SP5GW/RF_Tap/img/IMG_1132.jpg

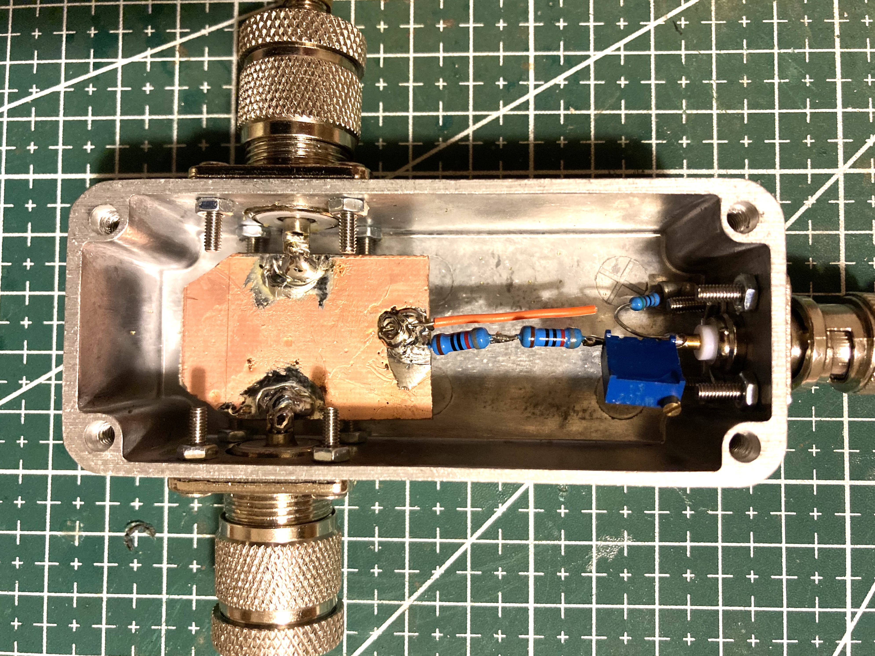
img/IMG_1132.jpg
