SP5GW/RF_Tap/meas/S21_RF_Input_RF_Tap_noCap_UnTerm2024-03-03 11-43-42.png

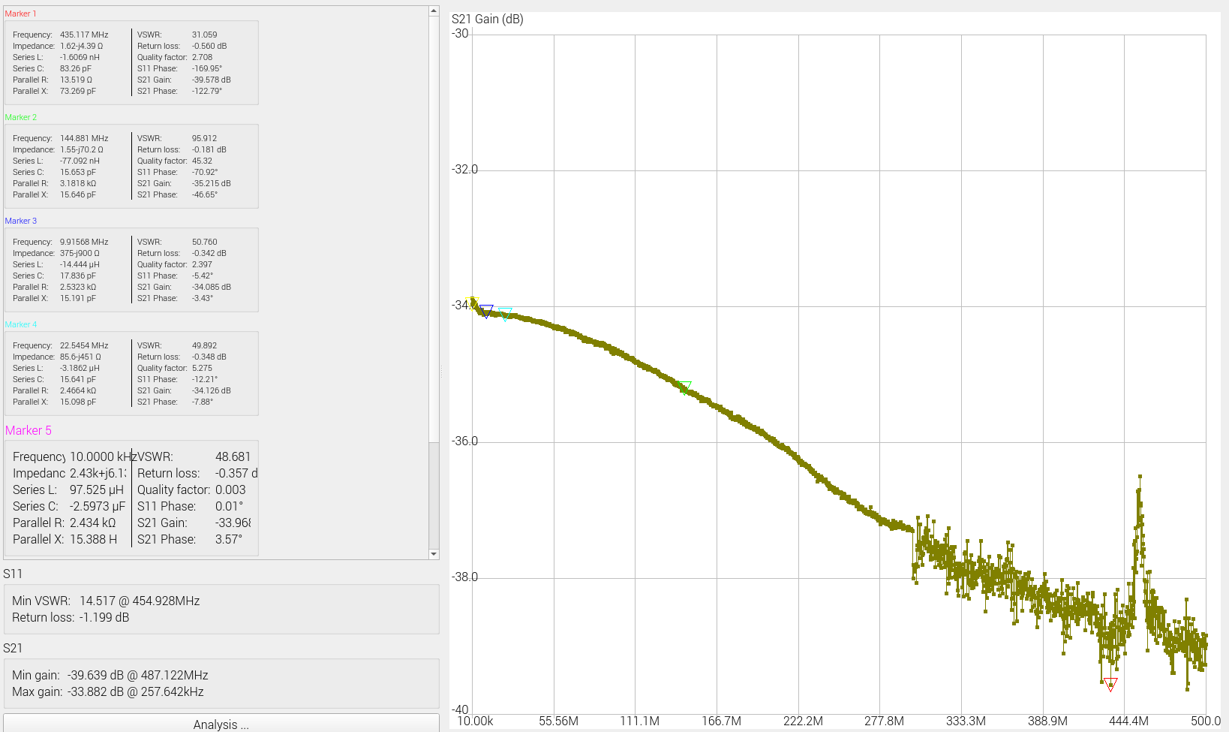
meas/S21_RF_Input_RF_Tap_noCap_UnTerm2024-03-03 11-43-42.png
