SP5GW/RF_Tap/sim/RFTap_v1_calibration_circuit.asc

Rs_nanovna_ch0: res; 50
Rs_nanovna_ch1: res; 50
V1: signal; AC 1
Named nets: 0, v1, Uin
.ac dec 1000 1k 100Meg
.step param R list 100Meg 50
.param R 5000
1) NanoVNA Callibration Circuit (through)
Calibration_Adj = Uin/v1 = 0.5/1=0.5 (-6dB)
