SP5GW/RF_Tap/sim/RFTap_v1_terminated_RF_Path.asc

DummyLoad: res; 50
R2: res; 51
R3: res; 2500
Rs_nanovna_ch0: res; 50
Rs_nanovna_ch1: res; 50
V1: signal; AC 2
Named nets: 0, v1, Uin, Utap
.ac dec 1000 1k 500Meg
3) NanoVNA S21 measurement (RF Path terminated with 50 ohm load)
Uin/v1 = 0.5/1=0.5 (-6dB) => Calibration_Adjustment = 6dB
V1 = 1V
Uin = 0.4951V
Utap = 4.951mV
Utap/V1 = 0.04951 (-46.106dB)
 
Logmag_NanoVna_Reading [dB] = Utap/V1 [dB] + 
Calibration_Adjustment [dB] = -46.106 + 6 = -40.106dB
 
Utap/Uin = 0.01 (-40dB)
