SP5GW/RF_Tap/sim/RFTap_v1_terminated_RF_Path_100W.asc

DummyLoad: res; 50
R1a: res; 820
R1b: res; 820
R1c: res; 820
R2: res; 51
Rs_nanovna_ch0: res; 50
Rs_nanovna_ch1: res; 50
V1: voltage; 100
Named nets: 0, v1, Uin, Utap, Vr1a, Vr1b
4) Resistor Power Rating Calculation
.op
Power dissipated in a purely resistive load fed from an AC rms supply 
is the same as that for a resistor connected to a DC supply and is 
given as, i.e.:
P = Urms*Irms where Irms = Urms/R
this gives:
P=Urms^2/R
 
Urms = Upk / SQRT(2) where Upk is peak voltage, while Urms is 
root-mean-sqaure voltage
.tran 5u
For instantaneous power Ppk=100W and 50ohm resistive load:
 
Upk = SQRT(Ppk*R) = SQRT(100*50) = 70.7V
Urms = Upk/SQRT(2) = SQRT(Ppk*R/2) = SQRT(100*50/2) = 50V
 
If Urms applied to dummylaod = 50V then the power disipating 
on resistor network is:
 
Prms(R1a or R1b or R1c) = 325mW (minimum R1a, R1b, R1c  resistor rating is 500mW)
Prms(R2) = 5mW (minimum R2 resistor rating can be 125mW)
