SP5GW/RF_Tap/sim/RFTap_v1_terminated_RF_Path_FreqDepLoss.asc

C: cap; {x}
Cparasitic: cap; 14p
DummyLoad: res; 50
R1a: res; 820
R1b: res; 820
R1c: res; 820
R2: res; 51
Rs_nanovna_ch0: res; 50
Rs_nanovna_ch1: res; 50
V1: signal; AC 2
Named nets: 0, v1, Uin, Utap
.ac dec 1000 1Meg 500Meg
3) NanoVNA S21 measurement (RF Path terminated with 50 ohm load) - frequency dependent loss
f=3.52MHz   => -40.1dB
f=144.0MHz => -40.5dB
f=435.1MHz => -42.9dB
.step param x list 0.00001p 0.7p
