SP5GW/RF_Tap/sim/RFTap_v1_unterminated_RF_Path.asc

R2: res; 51
R3: res; 2500
Rs_nanovna_ch0: res; 50
Rs_nanovna_ch1: res; 50
V1: signal; AC 1
Named nets: 0, v1, Uin, Utap
.ac dec 1000 1k 100Meg
2) NanoVNA S21 measurement (RF Path unterminated)
Uin/v1 = 0.5/1=0.5 (-6dB) => Calibration_Adjustment = 6dB
V1 = 1V
Uin = 0.981V
Utap = 9.804mV
Utap/V1 = 0.09804 ( -40.172dB)
Logmag_NanoVna_Reading [dB] = Utap/V1 [dB] + Calibration_Adjustment [dB] = 
-40.172 + 6 = -34.172dB
 
Utap/Uin = 0.01 (-40dB)
