SP5GW/RF_Tap/schematics/RF_Tap_Schematics.kicad_sch

## KiCad design schematics/RF_Tap_Schematics.kicad_sch (2024-03-12)

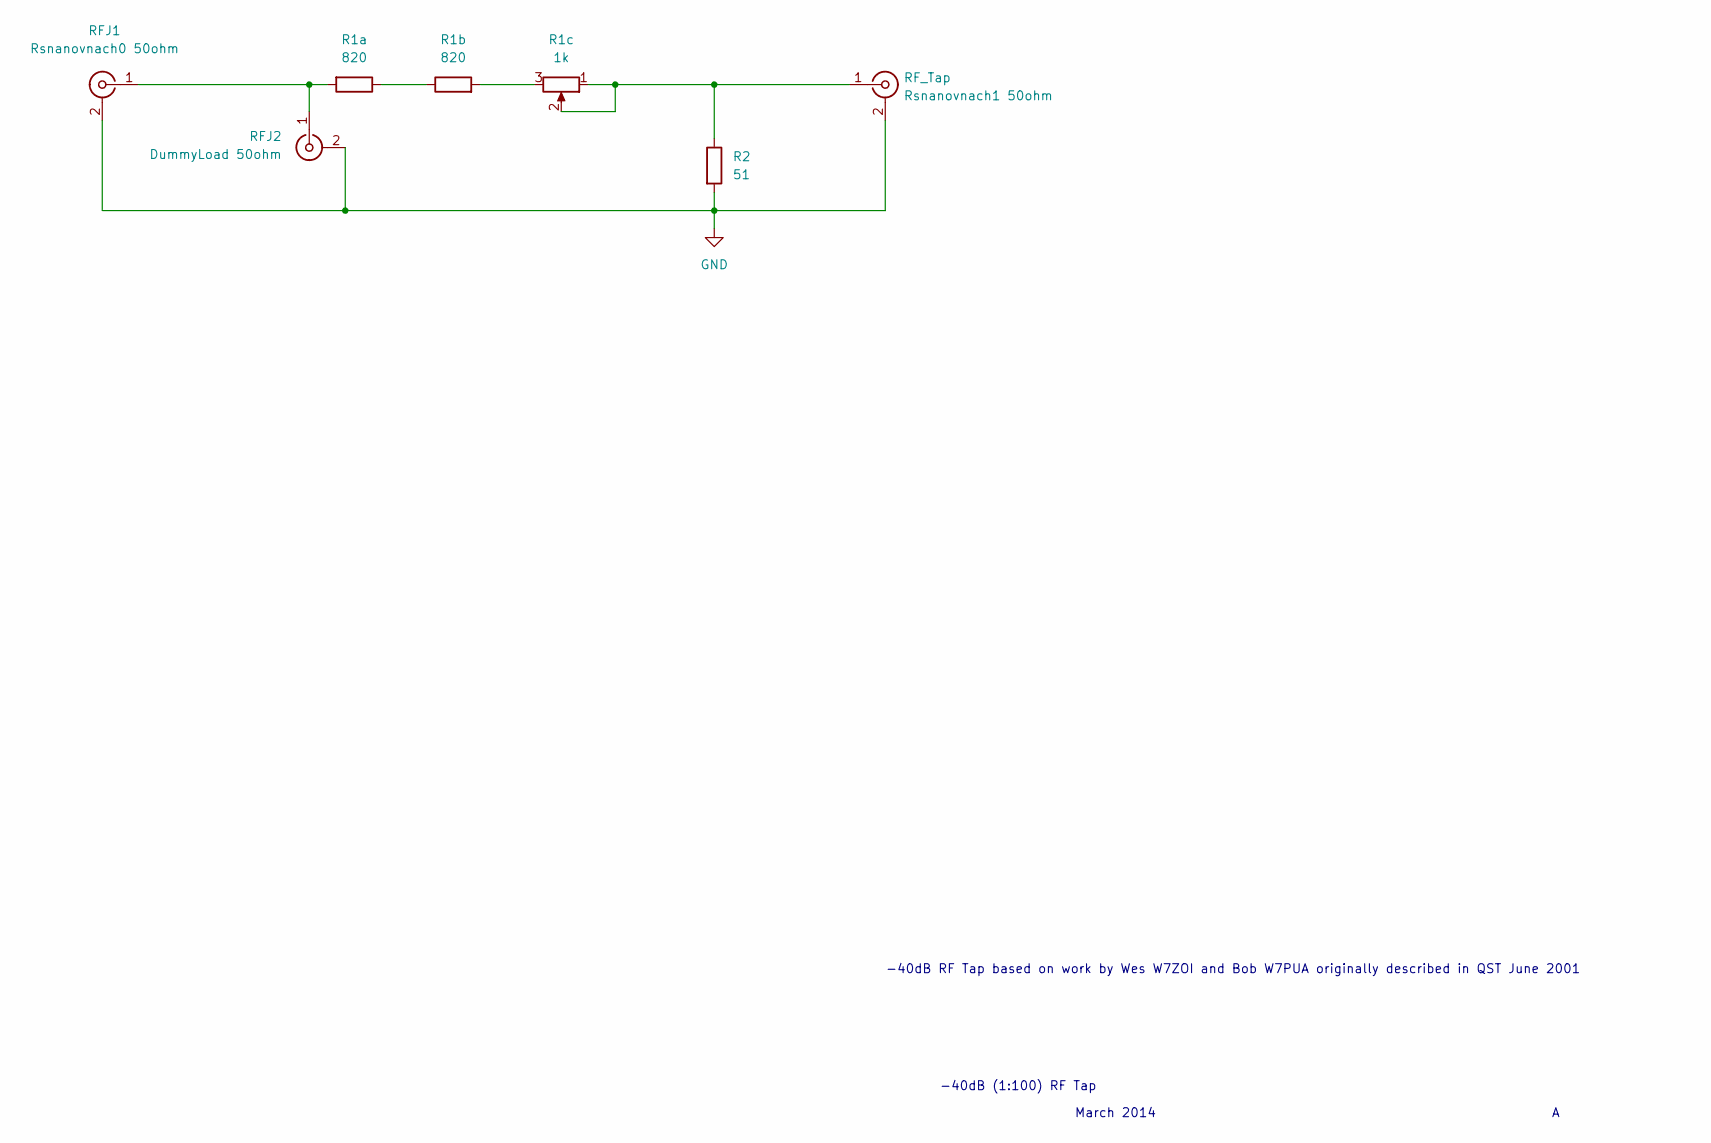
[picture p24: schematic RF_Tap_Schematics.kicad_sch]

Parts:
R1a, R1b: 820
R1c: 1k
R2: 51
RFJ1: Rsnanovnach0 50ohm
RFJ2: DummyLoad 50ohm
RF_Tap: Rsnanovnach1 50ohm

Connections:
GND: R2.2, RFJ1.2 (Ext), RFJ2.2 (Ext), RF_Tap.2 (Ext)
unnamed: R1a.1, R1b.1
unnamed: R1a.2, RFJ1.1 (In), RFJ2.1 (In)
unnamed: R1b.2, R1c.3
unnamed: R1c.1, R1c.2, R2.1, RF_Tap.1 (In)

Notes on the sheet:
-40dB (1:100) RF Tap
March 2014
-40dB RF Tap based on work by Wes W7ZOI and Bob W7PUA originally described in QST June 2001
